SaahilParikh/Quadcopter/src/apps/Quadcopter_Final/flight_controller.h

#pragma once
#include "nrf_twi_mngr.h"
#include "mag.h"
#include "lsm9ds1.h"
#include "accel.h"
#include "pid.h"

// SETUP FOR SENSORS
orientation_data current_orient;

lsm9ds1_measurement_t gyro_v;
accel_angles_t accel_d;
mag_angles_t mag_d;
lsm9ds1_measurement_t gyro_d;
// END OF SENSORS SET UP

#define pwm_update_rate 2
float COPTER_MASS;

extern PID_Controller pitch_displacement;
extern PID_Controller roll_displacement;
extern PID_Controller yaw_displacement;

extern PID_Controller pitch_velocity;
extern PID_Controller roll_velocity;
extern PID_Controller yaw_velocity;

void init_sensors(void);
void init_flight_controller(void);
void arm(void);
void fly(void);
void kill(void);
void fly_w_o_sensorget(void);
