SaahilParikh/Quadcopter/src/apps/Quadcopter_Final/pid.h

#pragma once

typedef struct {
	float kP;
	float kI;
	float kD;
}	Controller_Constants;

typedef struct {
	float error;
	float target;
	
	float integral;
	float integral_bound;

	float derivitive;
	float prev_error;

	float time_step;

	Controller_Constants constants;
}	PID_Controller;

float step(PID_Controller* controller, float current);
void init_controller(PID_Controller* controller, Controller_Constants *kConst, float dt, float integral_max);
void update_target(PID_Controller* controller, float new_target);
